SparkMakerspace/YakBak-soldering-kit/Photos/photo_2023-05-06_11-19-56 (2).jpg

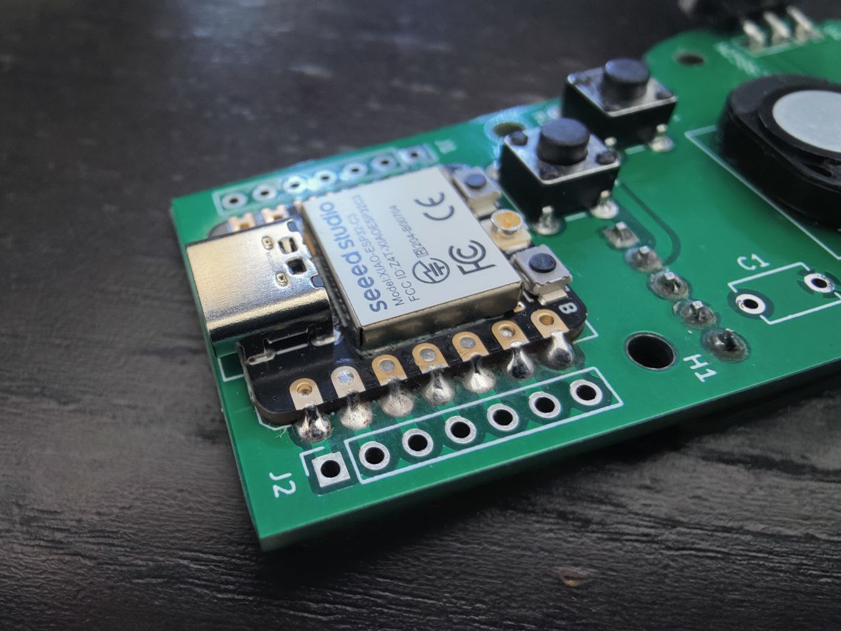
Photos/photo_2023-05-06_11-19-56 (2).jpg
