SparkMakerspace/YakBak-soldering-kit/Photos/photo_2023-05-06_11-27-19.jpg

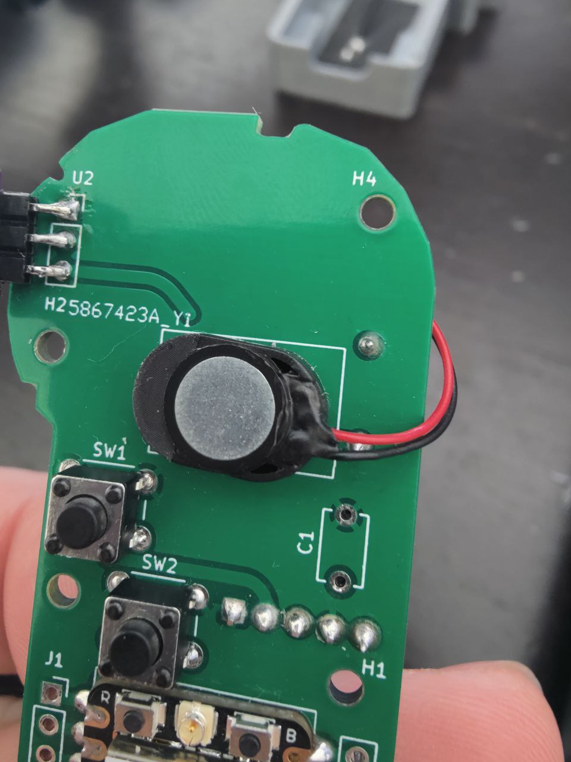
Photos/photo_2023-05-06_11-27-19.jpg
