SparkMakerspace/YakBak-soldering-kit/enclosure/Yak Spark Board.FCStd

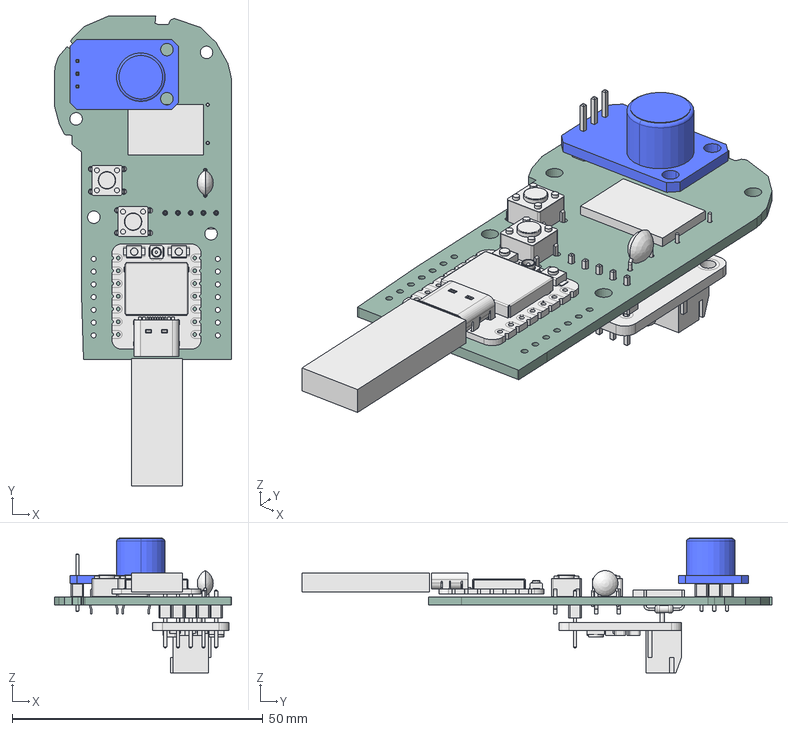
[picture p17: CAD file, 2023-04-21]
enclosure/Yak Spark Board.FCStd
35.3 x 93.7 x 26.8 mm
PCB
